asanza/keithley_199/src/sys/adcctrl.h

/*
 * adcseq.h
 *
 * Copyright (c) ${year}, Diego F. Asanza. All rights reserved.
 *
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
 * Created on January 18, 2015, 2:05 AM
 */

/** ADC Control is done by using sequences. 
 * The adc on the keithley 199 is controlled by a 32 bit shift register.
 * This shift register controls which input and range is selected, furthermore
 * it also controls the adc conversion.
 * 
 * A serie of shift register values used to perform an analog digital conversion
 * for a given input settings is called an adc_control_sequence
 * 
 * ADC_INPUT defines all possible input configurations on the Keithley.
 * ADC_RANGE defines all possible range configurations.
 * 
 * Of course, not all ranges are possible in some inputs. For example, when using
 * the input configuration for 3V, only ranges from 300m to 300 are available.
 * 
 * In order to get the adc_control sequence needed to perform an adc conversion 
 * for a given input configuration and range, call the function adc_ctrl_get_sequence.
 * This returns a pointer to the first element on the sequence. This sequence is used
 * by the functions in adc.c in order to perform a conversion.
 * 
 */

#ifndef ADCCTRL_H
#define	ADCCTRL_H

#ifdef	__cplusplus
extern "C" {
#endif
#include <stdint.h>

    typedef enum{
    ADC_INTEGRATION_50HZ = 20000, /**< 20mS or 50Hz */
    ADC_INTEGRATION_60HZ = 16667, /**< 16mS or 60Hz  */
}adc_integration_period;

typedef enum {
    ADC_CHANNEL_0 = 0x00,
    ADC_CHANNEL_1 = 0x01,
    ADC_CHANNEL_2 = 0x02,
    ADC_CHANNEL_3 = 0x04,
    ADC_CHANNEL_4 = 0x08,
    ADC_CHANNEL_5 = 0x10,
    ADC_CHANNEL_6 = 0x20,
    ADC_CHANNEL_7 = 0x40,
    ADC_CHANNEL_8 = 0x80,
    ADC_NUMBER_OF_CHANNELS,
}adc_channel;
    
typedef enum {
        ADC_INPUT_VOLTAGE_DC = 0x00,
        ADC_INPUT_VOLTAGE_AC,
        ADC_INPUT_CURRENT_DC,
        ADC_INPUT_CURRENT_AC,
        ADC_INPUT_RESISTANCE_2W,
        ADC_INPUT_RESISTANCE_4W,
        ADC_NUMBER_OF_INPUTS /**< number of valid inputs */
}adc_input;

typedef enum {
    ADC_RANGE_30m = 0x00,
        ADC_RANGE_300m,
        ADC_RANGE_3,
        ADC_RANGE_30,
        ADC_RANGE_300,
        ADC_RANGE_3K,
        ADC_RANGE_30K,
        ADC_RANGE_300K,
        ADC_RANGE_3M,
        ADC_RANGE_30M,
        ADC_RANGE_300M,
        ADC_RANGE_COUNT,
} adc_range;
    
typedef struct hal_adc_integration_sequence_t adc_control_sequence;

/* reset control sequence.*/
void adcctrl_reset(adc_control_sequence* sequence);

/* get the next control sequence for given adc settings. */
uint32_t adcctrl_get_next_sequence(adc_control_sequence* sequence);

/* get the hardware adc settings for the selected input and range. 
 * Return null if selected input and range are not supported in the 
 * hardware. */
adc_control_sequence* adcctrl_get_sequence(adc_input input, adc_range range);

/** Get a unique identifier for each supported hardware configuration, or -1 if
 * hardware configuration is not supported. */
int adcctrl_get_sequence_id(adc_input input, adc_range range);

adc_range adcctrl_get_next_range(adc_input input, adc_range actual_range);
adc_range adcctrl_get_previous_range(adc_input input, adc_range actual_range);

#ifdef	__cplusplus
}
#endif

#endif	/* ADCSEQ_H */
