asanza/keithley_199/src/tasks/tskmgr.c

/*
 * tskmgr.c
 *
 * Copyright (c) 2015, Diego F. Asanza. All rights reserved.
 *
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
 * Created on August 23, 2015, 7:30 PM
 */

#include "tskmgr.h"
#include <settings.h>
#include <system.h>
#include <FreeRTOS.h>
#include <task.h>
#include <diag.h>
#include <assert.h>
#include <dispkyb.h>
#include <queue.h>
#include <adcdefs.h>
#include <ctype.h>

#define SYSTEM_TASK_STACK_SIZE      300
#define WLAN_TASK_STACK_SIZE        200
#define SCPI_TASK_STACK_SIZE        600
#define TASK_STACK_SIZE             400
#define SYSTEM_TASK_PRIORITY        2
#define SCPI_TASK_PRIORITY          3
#define TASK_PRIORITY               3
#define MESSAGE_DELAY               500

typedef enum {
    TASK_MULTIMETER,
    TASK_CALIBRATION,
    TASK_COUNT
} sys_task_t;

extern task_iface_t multimeter_task;
extern task_iface_t calibration_task;

static task_iface_t* running_task = NULL;

static void system_task(void* params);
extern void scpi_task(void* params);

static void sys_init(void);
static void load_settings();
static void start_task(sys_task_t task);
static void apply_settings();
static void poll_key(void);

void taskmgr_start(void)
{
    xTaskCreate(system_task, "SYS", SYSTEM_TASK_STACK_SIZE, NULL,
        SYSTEM_TASK_PRIORITY, NULL);
    xTaskCreate(scpi_task, "SCPI", SCPI_TASK_STACK_SIZE, NULL,
        SCPI_TASK_PRIORITY, NULL);
    xTaskCreate(multimeter_task.task, "MUL", TASK_STACK_SIZE, NULL, TASK_PRIORITY,
        multimeter_task.handler);
    vTaskSuspend(*multimeter_task.handler);
}

static void system_task(void* pvParameters)
{
    sys_init();
    // Reload Sysstate from eeprom.
    load_settings();
    while (1) {
        vTaskDelay(10);
        if (!running_task->handler) {
            running_task = &multimeter_task;
            running_task->resume();
        }
        if(running_task->has_keys){
            continue;
        }
        poll_key();
    }
}

static void start_task(sys_task_t task)
{
    switch (task) {
        case TASK_MULTIMETER: 
            multimeter_task.resume();
            running_task = &multimeter_task;
            break;
        case TASK_CALIBRATION:
            assert(running_task != NULL);
            xTaskCreate(calibration_task.task, "CAL", TASK_STACK_SIZE, NULL, TASK_PRIORITY,
                calibration_task.handler);
            running_task = &calibration_task;
            break;
        default:
            assert(0);
    }
}

static void sys_init(void)
{
    DIAG("Initializing System");
    display_kyb_init(); /* should be started after os starts */
    int i = 0;
    char* temp = REPOVERSION;
    while (temp[i] != 0) {
        display_putc(toupper(temp[i]), i);
        i++;
    }
    vTaskDelay(MESSAGE_DELAY / portTICK_PERIOD_MS); // show firmware version at startup.
}

static void load_settings()
{
    settings_init();
    if (settings_restore(SETTINGS_0)) {
        display_clear();
        DIAG("Bad Settings on Store. Loading defaults");
        display_puts("SETT ERROR");
        vTaskDelay(MESSAGE_DELAY / portTICK_PERIOD_MS);
    }
    int integration_period = settings_get_integration_period();
    DIAG("i period: %d", integration_period);
    switch (integration_period) {
            display_clear();
        case ADC_INTEGRATION_50HZ: display_puts("FREQ=50 HZ");
            break;
        case ADC_INTEGRATION_60HZ: display_puts("FREQ=60 HZ");
            break;
        default:
            assert(0);
    }
    vTaskDelay(MESSAGE_DELAY / portTICK_PERIOD_MS);
    display_clear();
    apply_settings();
    switch (settings_get_input()) {
        case ADC_INPUT_CURRENT_DC:
        case ADC_INPUT_CURRENT_AC:
        case ADC_INPUT_RESISTANCE_2W:
        case ADC_INPUT_VOLTAGE_DC:
        case ADC_INPUT_VOLTAGE_AC:
        case ADC_INPUT_TEMP:
            start_task(TASK_MULTIMETER);
            break;
        default:
            assert(0);
    }
}

static void apply_settings()
{
    display_puts(" ------- ");
    if (!calibration_restore()) {
        DIAG("CAL ERROR");
        display_clear();
        display_puts("CAL ERROR");
        vTaskDelay(MESSAGE_DELAY / portTICK_PERIOD_MS);
    }

    if (system_set_configuration(settings_get_input(), settings_get_range(),
        settings_get_integration_period(), settings_get_channel(),
        calibration_gain(), calibration_offset(), settings_get_resolution())) {
        display_clear();
        display_puts("NOT IMPL");
        vTaskDelay(MESSAGE_DELAY / portTICK_PERIOD_MS);
        display_clear();
    }
    if (settings_is_autorange())
        display_setmode(DISP_AC);
    else
        display_clearmode(DISP_AC);
}

bool shift_key = false;
bool repeat_key = true;

static void poll_key(void)
{
    key_id key = display_wait_for_key();
    switch (key) {
        case KEY_0:break;
        case KEY_1:break;
        case KEY_2:break;
        case KEY_3:
            if (shift_key) {
                adc_resolution res = settings_get_resolution();
                res++;
                if (res >= ADC_MAX_RESOLUTION)
                    res = ADC_RESOLUTION_5_5;
                settings_set_resolution(res);
                shift_key = false;
            } else {
                if (settings_get_input() == ADC_INPUT_TEMP) return;
                if (settings_is_autorange()) {
                    settings_set_autorange(false);
                } else {
                    settings_set_autorange(true);
                }
            }
            running_task->pause();
            apply_settings();
            running_task->resume();
            break;
        case KEY_4:
            if (repeat_key == false) break;
            shift_key = !shift_key;
            if (shift_key)
                repeat_key = false;
            break;
        case KEY_5:
            if (shift_key) {
                settings_set_input(ADC_INPUT_RESISTANCE_4W);
            } else {
                settings_set_input(ADC_INPUT_RESISTANCE_2W);
            }
            shift_key = false;
            running_task->pause();
            apply_settings();
            running_task->resume();
            break;
        case KEY_6:
            if (shift_key) {
                settings_set_input(ADC_INPUT_VOLTAGE_AC);
                shift_key = false;
            } else{
                settings_set_input(ADC_INPUT_VOLTAGE_DC);
            }
            running_task->pause();
            apply_settings();
            running_task->resume();
            break;
        case KEY_7:
            if (shift_key) {
                settings_set_input(ADC_INPUT_CURRENT_AC);
                shift_key = false;
            } else
                settings_set_input(ADC_INPUT_CURRENT_DC);
            running_task->pause();
            apply_settings();
            running_task->resume();
            break;
        case KEY_8:
            if (shift_key) {
                shift_key = false;
            } else{
                settings_set_input(ADC_INPUT_TEMP);
                settings_set_autorange(false);
            running_task->pause();
            apply_settings();
            running_task->resume();
            }
            break;
        case KEY_9:
            running_task->pause();
            if (!shift_key) {
                display_puts("LOAD 0-9?");
                key = display_wait_for_key();
                key = display_wait_for_key();
                display_puts(" WORKING ");
                if (key <= 9)
                    settings_restore(key);
            } else {
                shift_key = false;
                display_puts("SAVE 0-9?");
                key = display_wait_for_key();
                key = display_wait_for_key();
                display_puts(" WORKING ");
                if (key <= 9)
                    settings_save(key);
            }
            apply_settings();
            running_task->resume();
            break;
        case KEY_UP:
            settings_range_up();
            settings_set_autorange(false);
            running_task->pause();
            apply_settings();
            running_task->resume();
            break;
        case KEY_DOWN:
            settings_range_down();
            settings_set_autorange(false);
            running_task->pause();
            apply_settings();
            running_task->resume();
            break;
        case KEY_CAL:
            running_task->pause();
            start_task(TASK_CALIBRATION);
            break;
        case KEY_NONE:
            repeat_key = true;
            break;
        default:
            Nop();
    }
    if (shift_key) {
        display_setmode(DISP_ZERO);
    } else {
        display_clearmode(DISP_ZERO);
    }
}
