asanza/keithley_199/src/sys/src/system.c

/*
 * sysstate.c
 *
 * Copyright (c) 2015, Diego F. Asanza. All rights reserved.
 *
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
 * Created on January 23, 2015, 9:04 PM
 */
#include <hal.h>
#include <usb_uart.h>
#include <assert.h>
#include <stddef.h>
#include <string.h>
#include <system.h>
#include <diag.h>
#include <math.h>
#include <adc.h>
#include "strutils.h"
#include "strutils.h"
#include "tmp275.h"
#include <FreeRTOS.h>
#include <semphr.h>

static SemaphoreHandle_t syslock;

static adc_channel channel = 0;
static double gain;
static double offset;

static double acc_value;

static bool is_temp_mode;

static adc_resolution resln;
static double wn_delta;

#define RESLN_6_5_FILTER_SIZE 10.0

static int set_configuration(adc_input input, adc_range range, 
    adc_integration_period period, adc_channel _channel, double _gain, double _offset,
    adc_resolution res){
        /* try to get syslock. Syslock shall be obtained before calling this function. */
    if(input == ADC_INPUT_TEMP){
        is_temp_mode = true;
    }else{
        is_temp_mode = false;
        adc_error err = adc_init(period, input, range);
        if (err != ADC_ERROR_NONE){
            return -1;
        }
    }
    channel = _channel;
    gain = _gain;
    offset = _offset;
    resln = res;
    switch(range){
        case ADC_RANGE_30m:
        case ADC_RANGE_30:
        case ADC_RANGE_30K:
        case ADC_RANGE_30M:
            wn_delta =  1e-4;
            break;
        case ADC_RANGE_3:
        case ADC_RANGE_3K:
        case ADC_RANGE_3M:
            wn_delta = 1e-5;
            break;
        case ADC_RANGE_300m:
        case ADC_RANGE_300:
        case ADC_RANGE_300K:
        case ADC_RANGE_300M:
            wn_delta = 1e-3;
            break;
        default: assert(0);
    }
    return 0;
}

int system_set_configuration(adc_input input, adc_range range,
    adc_integration_period period, adc_channel _channel, double _gain, double _offset,
    adc_resolution res)
{
    xSemaphoreTake(syslock, portMAX_DELAY);
    int ret = set_configuration(input, range, period, _channel, _gain, _offset, res);
    xSemaphoreGive(syslock);
    return ret;
}

double system_read_temp(void){
    double temperature;
    xSemaphoreTake(syslock, portMAX_DELAY);
    temperature = tmp245_read_temp_double();
    xSemaphoreGive(syslock);
    return temperature;
}

double system_get_max(adc_range range){
    return adc_get_max(range);
}


double system_read_input(system_flags_t* flag)
{
    if(xSemaphoreTake(syslock, 1000) == pdFALSE){
        DIAG("Cannot obtain sysmutex");
        return 0;
    }
    /* get lock before doing a measurement. It guarantees that no settings changes
     * are done while using the adc. */
    double value, temperature;
    *flag = 0;
    if(is_temp_mode){
        temperature = tmp245_read_temp_double();
        value = temperature;
    } else{
        value = gain * adc_read_value(channel, (int*)flag) + offset;
        if(resln == ADC_RESOLUTION_6_5){
            if(fabs(value - acc_value) <= wn_delta){
                acc_value = acc_value + (value - acc_value)/RESLN_6_5_FILTER_SIZE;
                value = acc_value;
            }else{
                *flag |= SYS_FLAG_FILTER_OUT_WINDOW;
                acc_value = value;
            }
        }
    }
    /* release semaphore when done. */
    xSemaphoreGive(syslock);
    assert(!isnan(value));
    assert(!isinf(value));
    return value;
}

void system_init(void)
{
    hal_sys_init();
    hal_i2c_init();
    usb_uart_init();
    tmp245_init();
    /* initialize system lock */
    syslock = xSemaphoreCreateMutex();
    set_configuration(ADC_INPUT_VOLTAGE_DC, ADC_RANGE_300, 
        ADC_INTEGRATION_50HZ, ADC_CHANNEL_0, 1, 0, ADC_RESOLUTION_5_5);
}
