asanza/keithley_199/src/hal/hal_sys.c

#include <hal_sys.h>
#include "HardwareProfile.h"
#include <peripheral/system.h>
#include <peripheral/uart.h>
#include <peripheral/ports.h>
#include <peripheral/power.h>
#include <diag.h>

void hal_sys_init(){
    SYSTEMConfigPerformance(SYS_CLK);
    INTSetVectorPriority(INT_VECTOR_UART(UART3),3);
    INTSetVectorPriority(INT_VECTOR_UART(UART5), 3);
    INTConfigureSystem(INT_SYSTEM_CONFIG_MULT_VECTOR);
    INTDisableInterrupts();
}

void hal_sys_idle(){
    PowerSaveIdle();
}

/* set the default interrupt handler for further analysis. */
void __attribute__((nomips16)) _DefaultInterrupt(void){
    DIAG("WARN: Default Interrupt\n");
}
