asanza/keithley_199/src/hal/fuses.c

/** @fuses.c
 * @brief Pic32 Configuration Bits.
 * @copyright (c) 2014 Diego F. Asanza
 * @Author: Diego F. Asanza
 *
 * This file contains the pic32 microcontroller fuses configuration.
 */

#include <xc.h>

// DEVCFG3
// USERID = No Setting
#pragma config FSRSSEL = PRIORITY_7     // Shadow Register Set Priority Select (SRS Priority 7)
#pragma config PMDL1WAY = ON            // Peripheral Module Disable Configuration (Allow only one reconfiguration)
#pragma config IOL1WAY = ON             // Peripheral Pin Select Configuration (Allow only one reconfiguration)

// DEVCFG2
#pragma config FPLLIDIV = DIV_2         // PLL Input Divider (2x Divider)
#pragma config FPLLMUL = MUL_20         // PLL Multiplier (20x Multiplier)
#pragma config FPLLODIV = DIV_1         // System PLL Output Clock Divider (PLL Divide by 1)

// DEVCFG1
#pragma config FNOSC = PRIPLL           // Oscillator Selection Bits (Primary Osc w/PLL (XT+,HS+,EC+PLL))
#pragma config FSOSCEN = OFF            // Secondary Oscillator Enable (Disabled)
#pragma config IESO = ON                // Internal/External Switch Over (Enabled)
#pragma config POSCMOD = XT             // Primary Oscillator Configuration (XT osc mode)
#pragma config OSCIOFNC = OFF           // CLKO Output Signal Active on the OSCO Pin (Disabled)
#pragma config FPBDIV = DIV_1           // Peripheral Clock Divisor (Pb_Clk is Sys_Clk/1)
#pragma config FCKSM = CSDCMD           // Clock Switching and Monitor Selection (Clock Switch Disable, FSCM Disabled)
#pragma config WDTPS = PS1048576        // Watchdog Timer Postscaler (1:1048576)
#pragma config WINDIS = OFF             // Watchdog Timer Window Enable (Watchdog Timer is in Non-Window Mode)
#pragma config FWDTEN = OFF             // Watchdog Timer Enable (WDT Disabled (SWDTEN Bit Controls))
#pragma config FWDTWINSZ = WISZ_25      // Watchdog Timer Window Size (Window Size is 25%)

// DEVCFG0
#pragma config DEBUG = ON              // Background Debugger Enable (Debugger is Enabled)
#pragma config JTAGEN = ON              // JTAG Enable (JTAG Port Enabled)
#pragma config ICESEL = ICS_PGx1        // ICE/ICD Comm Channel Select (Communicate on PGEC1/PGED1)
#pragma config PWP = OFF                // Program Flash Write Protect (Disable)
#pragma config BWP = OFF                // Boot Flash Write Protect bit (Protection Disabled)
#pragma config CP = OFF                 // Code Protect (Protection Disabled)
