asanza/keithley_199/src/utils/src/util_ringbuff.c

/*
 * util_ringbuff.c
 *
 * Copyright (c) 2015, Diego F. Asanza. All rights reserved.
 *
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
 * Created on December 26, 2014, 3:13 AM
 */

#include "util_ringbuff.h"
#include <stddef.h>
#include <stdbool.h>

util_ringbuffer buffers[NUMBER_OF_RINGBUFFERS];

static unsigned int used_buffers = 0;

util_ringbuffer* util_ringbuffer_new(unsigned char* data_buffer,
            int buffer_size){
    if(used_buffers >= NUMBER_OF_RINGBUFFERS)
        return NULL; /* No memory available */
    buffers[used_buffers].elems = data_buffer;
    buffers[used_buffers].next = data_buffer;
    buffers[used_buffers].elem_count = 0;
    buffers[used_buffers].size = buffer_size;
    used_buffers++;
    return &buffers[used_buffers - 1];
}

int util_ringbuffer_put(util_ringbuffer* buffer, unsigned char data){
    /* check if buffer is full */
    if(buffer->elem_count >= buffer->size)
        return UTIL_RINGBUFFER_IS_FULL;
    /* put elem in buffer */
    *buffer->next = data;
    /* increment element counter */
    buffer->elem_count++;
    /* increment pointer */
    buffer->next++;
    /* check if out of bounds */
    if(buffer->next >= buffer->elems + buffer->size)
        buffer->next = buffer->elems;
    return 0;
}

int util_ringbuffer_get(util_ringbuffer* buffer, unsigned char* data){
    /* check if buffer is empty */
    if(buffer->elem_count <= 0)
        return UTIL_RINGBUFFER_IS_EMPTY;
    /* get first element */
    unsigned char* first;
    first = buffer->next - buffer->elem_count;
    /* check if out of bounds */
    if(first < buffer->elems)
    {
        int t = buffer->elems - first;
        first = buffer->elems + buffer->size - t;
    }
    /* decrement counter */
    buffer->elem_count --;
    /* return first element */
    *data = *first;
    return 0;
}

void utils_blocking_delay_ms(unsigned int ms){
    int i = 0;
    for(i = 0; i < ms*1000; i++){
        
    }
}
