asanza/keithley_199/test/test_util_ringbuff.c

#undef NUMBER_OF_RINGBUFFERS
#define NUMBER_OF_RINGBUFFERS 2

#include "unity.h"
#include "util_ringbuff.c"

#define BUFFSIZE 20

void setUp(void){
  /* clear buffer pool before reusing */
  used_buffers = 0;
}

void tearDown(void){
}

void test_ringbuff_new(void){
  util_ringbuffer* buff;
  unsigned char data[BUFFSIZE];
  buff = util_ringbuffer_new(data, BUFFSIZE); 
  TEST_ASSERT_NOT_EQUAL(NULL,buff);
  buff = util_ringbuffer_new(data, BUFFSIZE);
  TEST_ASSERT_NOT_EQUAL(NULL,buff);
  buff = util_ringbuffer_new(data, BUFFSIZE);
  TEST_ASSERT_EQUAL(NULL,buff);
}

void test_ringbuff_put_get(void){
  util_ringbuffer* buff;
  unsigned char data[BUFFSIZE];
  buff = util_ringbuffer_new(data, BUFFSIZE);
  TEST_ASSERT_NOT_EQUAL(NULL,buff);
  /* put data into buffer */
  unsigned char i = 0;
  while(util_ringbuffer_put(buff,i)!=UTIL_RINGBUFFER_IS_FULL){
    TEST_ASSERT_EQUAL(i,data[i]);
    i++;
  }
  /* get data from buffer */
  i = 0;
  unsigned char c;
  while(util_ringbuffer_get(buff,&c)!=UTIL_RINGBUFFER_IS_EMPTY){
    TEST_ASSERT_EQUAL(i,c);
    i++;
  }
  i = 0;
  while(util_ringbuffer_put(buff,i++)!=UTIL_RINGBUFFER_IS_FULL);
  i--;
  int j = 0, k = 8;
  while(k-- >= 0){
    unsigned char c;
    util_ringbuffer_get(buff,&c);
    TEST_ASSERT_EQUAL(j++,c);
  }
  while(util_ringbuffer_put(buff,i++)!=UTIL_RINGBUFFER_IS_FULL);
  i--;
  k = 12;
  while(k-- >= 0){
    unsigned char c;
    util_ringbuffer_get(buff, &c);
    TEST_ASSERT_EQUAL(j++,c);
  }
}
